HanSur94/SmartHomeEnvironmentLogger/Pasted image 20230129203700.png

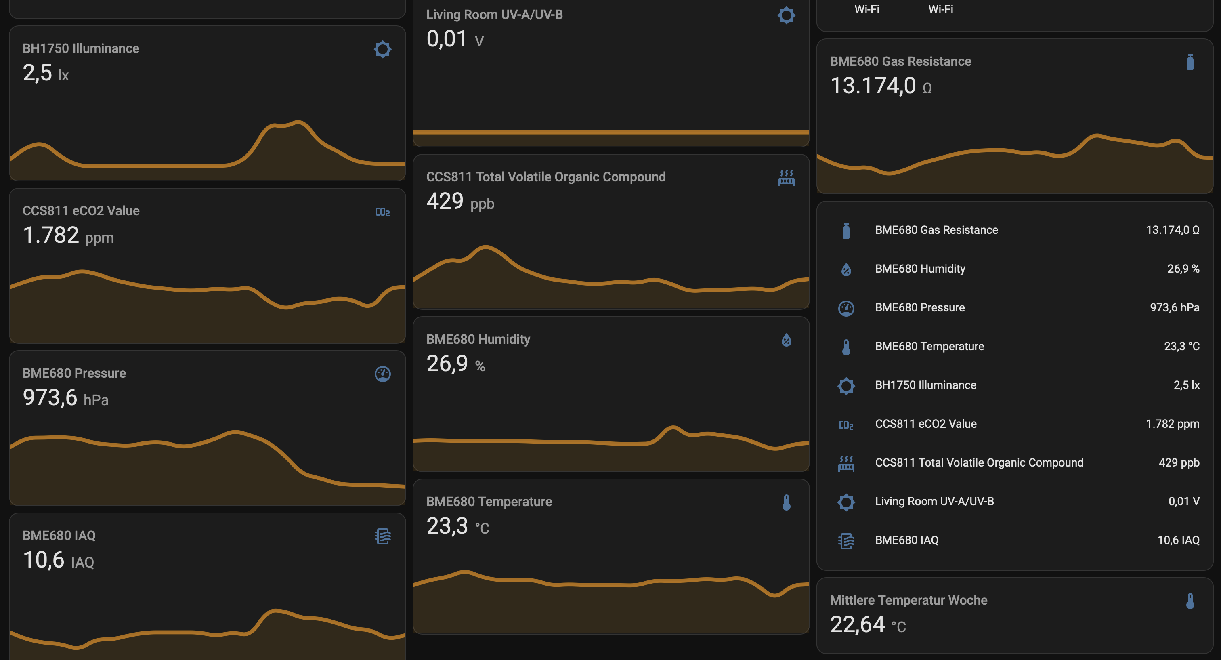
Pasted image 20230129203700.png
